ThomasBV67/ProjetChambreFroide/testCapteurs/testCapteurs.ino

/*
  testCapteurs
  Ce programme permet de tester l'aquisition de température des capteurs DS18B20 et d'envoyer 
  ces informations par des trames personalisées sur le port série.
 
  modifié le 26 janvier 2021
  par Thomas Bureau-Viens
 */
 
#include <OneWire.h> 
#include <DallasTemperature.h> 

// Data wire is plugged into digital pin 12 on the Arduino 
#define ONE_WIRE_BUS 4 


// Setup a oneWire instance to communicate with any OneWire device 
OneWire oneWire(ONE_WIRE_BUS);     


// Pass oneWire reference to DallasTemperature library 
DallasTemperature sensors(&oneWire); 


// variable to hold device addresses 
DeviceAddress Thermometer;   

// Variables globales
int g_deviceCount = 0; 
int g_checkSum = 0;
float g_tempC; 

void setup(void) 
{ 
  sensors.begin();    // Start up the library 

  Serial.begin(9600);   
  sensors.setResolution(12); // Résolution maximale

  g_deviceCount = sensors.getDeviceCount(); // Get le nombre de capteurs branchés
} 

void loop(void) 
{  
  char tempEntier, tempDecimal; // Variables tempon pour séparer la température en entier et décimale
  byte trame[12] = {};
  
  // Send command to all the sensors for temperature conversion 
  sensors.requestTemperatures();  

  // Display temperature from each sensor 

  for (int i = 0;  i < g_deviceCount;  i++) // Loop qui passe par chaque capteur
  { 
    sensors.getAddress(Thermometer, i); // Get l'address du capteur courant
    g_tempC = sensors.getTempCByIndex(i); // get la température 
    
    tempEntier = (char)g_tempC;
    tempDecimal = (g_tempC-tempEntier)*100;

    // Ajout du bit SOH à la trame
    trame[0] = 0x01;

    // Ajout de l'adresse du capteur à la trame
    for(int i = 0; i<8; i++)
    {
      trame[i+1] = Thermometer[i];
      g_checkSum = g_checkSum + Thermometer[i];
    }

    // Ajout de la température à la trame
    trame[9]=(byte)tempEntier; 
    g_checkSum += tempEntier;
    trame[10] = (byte)tempDecimal; 
    g_checkSum += tempDecimal;

    // Finalisation du CheckSum
    trame[11] = g_checkSum%0x100;

    
    for(int j = 0; j<12 ; j++)
    {
      Serial.println(trame[j]);
    }
    
  } 
  delay(2000); 

} 
